ksarkies/Remote-Power-Switch/gEDA-master-receiver/master-receiver-pcb.png

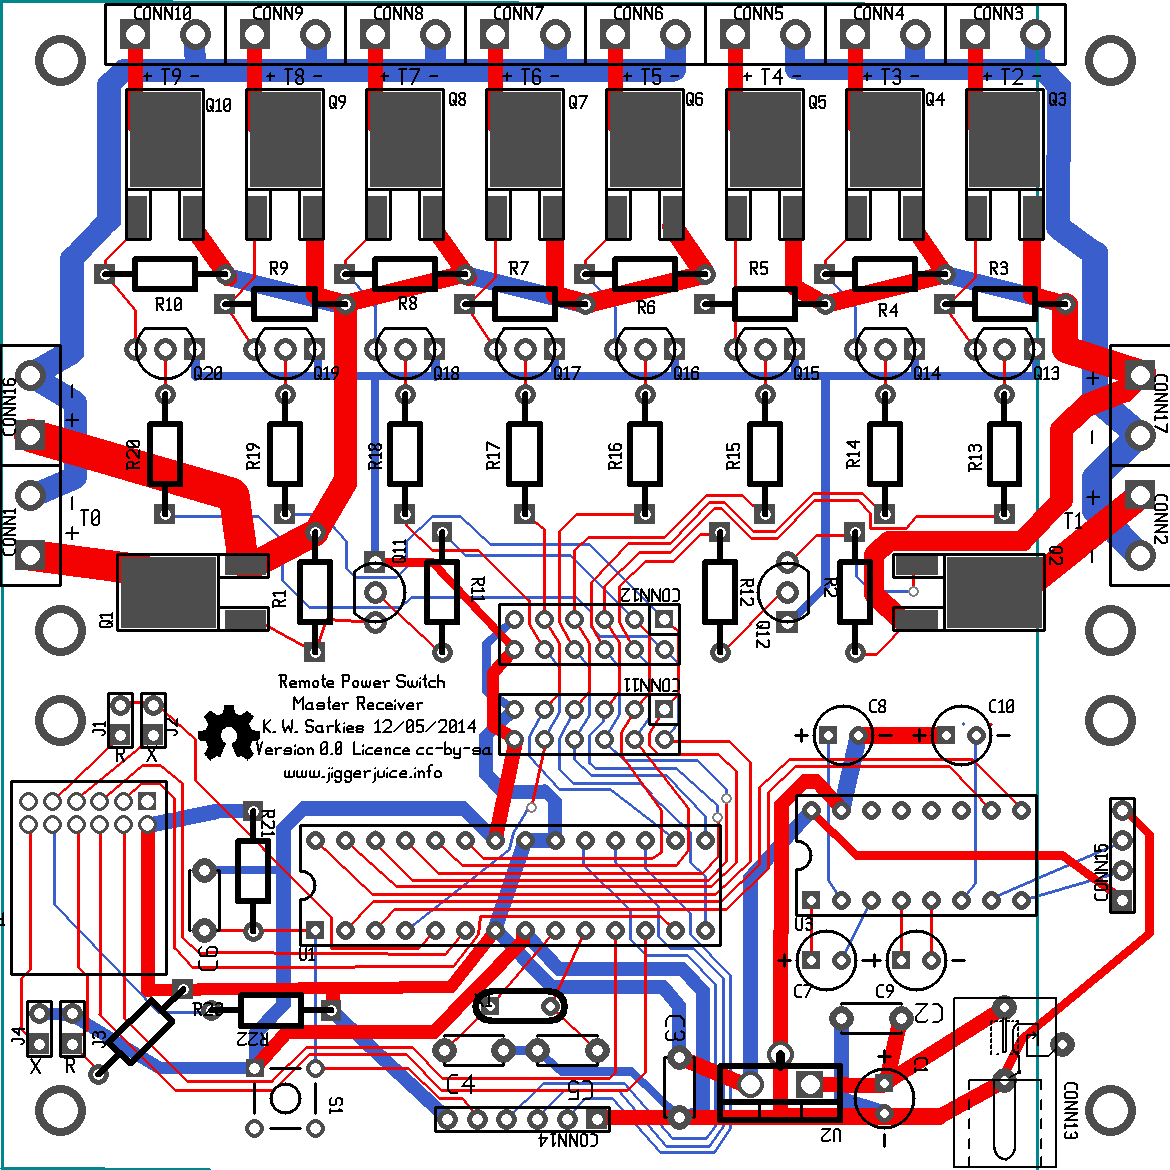
gEDA-master-receiver/master-receiver-pcb.png
