ksarkies/Remote-Power-Switch/gEDA-master-receiver/master-receiver-sw.png

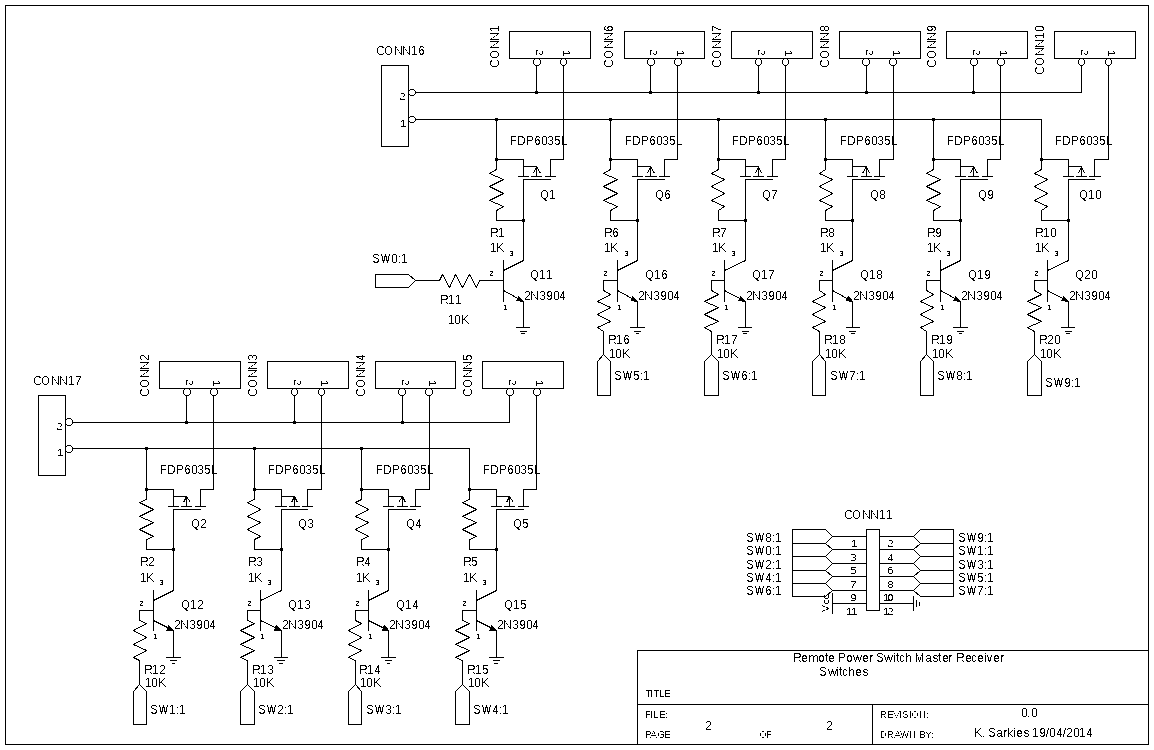
gEDA-master-receiver/master-receiver-sw.png
